MQ37/esp32-air-quality-monitor/firmware/components/lvgl_esp32_drivers/lvgl_tft/st7789.c

/**
 * @file st7789.c
 *
 * Mostly taken from lbthomsen/esp-idf-littlevgl github.
 */

#include "freertos/FreeRTOS.h"
#include "freertos/task.h"
#include "sdkconfig.h"

#include "esp_log.h"

#include "st7789.h"

#include "disp_spi.h"
#include "driver/gpio.h"

/*********************
 *      DEFINES
 *********************/
#define TAG "st7789"
/**********************
 *      TYPEDEFS
 **********************/

/*The LCD needs a bunch of command/argument values to be initialized. They are stored in this struct. */
typedef struct {
    uint8_t cmd;
    uint8_t data[16];
    uint8_t databytes; //No of data in data; bit 7 = delay after set; 0xFF = end of cmds.
} lcd_init_cmd_t;

/**********************
 *  STATIC PROTOTYPES
 **********************/
static void st7789_set_orientation(uint8_t orientation);

static void st7789_send_color(void *data, size_t length);

/**********************
 *  STATIC VARIABLES
 **********************/

/**********************
 *      MACROS
 **********************/

/**********************
 *   GLOBAL FUNCTIONS
 **********************/
void st7789_init(void)
{
    /*
     * Init sequence for the ST7789P3 IPS panel on the ESP32-32E / E32R32P board.
     * Register values match the panel vendor's example code; see
     * docs/display-init.md in the project root for background.
     * databytes: number of parameter bytes; bit 7 set = wait 100 ms afterwards.
     */
    lcd_init_cmd_t st7789_init_cmds[] = {
        {ST7789_MADCTL, {0x00}, 1},                     // memory access order; replaced by st7789_set_orientation() below
        {ST7789_COLMOD, {0x05}, 1},                     // 16 bits per pixel (RGB565)
        {ST7789_PORCTRL, {0x0C, 0x0C, 0x00, 0x33, 0x33}, 5}, // porch (blanking) timing
        {ST7789_GCTRL, {0x74}, 1},                      // gate driver voltages VGH/VGL
        {ST7789_VCOMS, {0x13}, 1},                      // VCOM voltage (vendor value; 0x23 was less stable here)
        {ST7789_LCMCTRL, {0x2C}, 1},                    // LCM control
        {ST7789_VDVVRHEN, {0x01}, 1},                   // take VDV/VRH from the next two commands
        {ST7789_VRHS, {0x10}, 1},                       // VRH: gamma reference voltage
        {ST7789_VDVSET, {0x20}, 1},                     // VDV: voltage offset
        {ST7789_FRCTR2, {0x0F}, 1},                     // frame rate in normal mode (0x0F = 60 Hz)
        {ST7789_PWCTRL1, {0xA4, 0xA1}, 2},              // power control 1 (AVDD/AVCL/VDS)
        {0xD6, {0xA1}, 1},                              // vendor-specific, kept as in the vendor code
        {ST7789_PVGAMCTRL, {0xD0, 0x07, 0x0E, 0x0B, 0x0A, 0x14, 0x38, 0x33, 0x4F, 0x37, 0x16, 0x16, 0x2A, 0x2E}, 14}, // positive gamma curve
        {ST7789_NVGAMCTRL, {0xD0, 0x0B, 0x10, 0x08, 0x08, 0x06, 0x35, 0x54, 0x4D, 0x0A, 0x14, 0x14, 0x2C, 0x2F}, 14}, // negative gamma curve
        {ST7789_EQCTRL, {0x11, 0x11, 0x03}, 3},         // equalize time control
#if ST7789_INVERT_COLORS == 1
        {ST7789_INVON, {0}, 0},                         // inversion on: needed for correct colours on this IPS panel
#else
        {ST7789_INVOFF, {0}, 0},
#endif
        {ST7789_SLPOUT, {0}, 0x80},                     // leave sleep mode, then wait
        {ST7789_DISPON, {0}, 0x80},                     // display on, then wait
        {0, {0}, 0xff},
    };

    //Initialize non-SPI GPIOs
    esp_rom_gpio_pad_select_gpio(ST7789_DC);
    gpio_set_direction(ST7789_DC, GPIO_MODE_OUTPUT);

#if !defined(ST7789_SOFT_RST)
    esp_rom_gpio_pad_select_gpio(ST7789_RST);
    gpio_set_direction(ST7789_RST, GPIO_MODE_OUTPUT);

    //Reset the display
    gpio_set_level(ST7789_RST, 0);
    vTaskDelay(100 / portTICK_PERIOD_MS);
    gpio_set_level(ST7789_RST, 1);
    vTaskDelay(100 / portTICK_PERIOD_MS);
#else
    // No reset GPIO: on the ESP32-32E the panel reset is tied to the ESP32 EN
    // pin, so send a software reset and give the controller time to restart.
    st7789_send_cmd(ST7789_SWRESET);
    vTaskDelay(150 / portTICK_PERIOD_MS);
#endif

    ESP_LOGI(TAG, "ST7789 initialization.");

    //Send all the commands
    uint16_t cmd = 0;
    while (st7789_init_cmds[cmd].databytes!=0xff) {
        st7789_send_cmd(st7789_init_cmds[cmd].cmd);
        st7789_send_data(st7789_init_cmds[cmd].data, st7789_init_cmds[cmd].databytes&0x1F);
        if (st7789_init_cmds[cmd].databytes & 0x80) {
                vTaskDelay(100 / portTICK_PERIOD_MS);
        }
        cmd++;
    }

    st7789_set_orientation(CONFIG_LV_DISPLAY_ORIENTATION);
}

/* The ST7789 display controller can drive up to 320*240 displays, when using a 240*240 or 240*135
 * displays there's a gap of 80px or 40/52/53px respectively. 52px or 53x offset depends on display orientation.
 * We need to edit the coordinates to take into account those gaps, this is not necessary in all orientations. */
void st7789_flush(lv_disp_drv_t * drv, const lv_area_t * area, lv_color_t * color_map)
{
    uint8_t data[4] = {0};

    uint16_t offsetx1 = area->x1;
    uint16_t offsetx2 = area->x2;
    uint16_t offsety1 = area->y1;
    uint16_t offsety2 = area->y2;

#if (CONFIG_LV_TFT_DISPLAY_OFFSETS)
    offsetx1 += CONFIG_LV_TFT_DISPLAY_X_OFFSET;
    offsetx2 += CONFIG_LV_TFT_DISPLAY_X_OFFSET;
    offsety1 += CONFIG_LV_TFT_DISPLAY_Y_OFFSET;
    offsety2 += CONFIG_LV_TFT_DISPLAY_Y_OFFSET;

#elif (LV_HOR_RES_MAX == 240) && (LV_VER_RES_MAX == 240)
    #if (CONFIG_LV_DISPLAY_ORIENTATION_PORTRAIT)
        offsetx1 += 80;
        offsetx2 += 80;
    #elif (CONFIG_LV_DISPLAY_ORIENTATION_LANDSCAPE_INVERTED)
        offsety1 += 80;
        offsety2 += 80;
    #endif
#elif (LV_HOR_RES_MAX == 240) && (LV_VER_RES_MAX == 135)
    #if (CONFIG_LV_DISPLAY_ORIENTATION_PORTRAIT) || \
        (CONFIG_LV_DISPLAY_ORIENTATION_PORTRAIT_INVERTED)
        offsetx1 += 40;
        offsetx2 += 40;
        offsety1 += 53;
        offsety2 += 53;
    #endif
#elif (LV_HOR_RES_MAX == 135) && (LV_VER_RES_MAX == 240)
    #if (CONFIG_LV_DISPLAY_ORIENTATION_LANDSCAPE) || \
        (CONFIG_LV_DISPLAY_ORIENTATION_LANDSCAPE_INVERTED)
        offsetx1 += 52;
        offsetx2 += 52;
        offsety1 += 40;
        offsety2 += 40;
    #endif
#endif

    /*Column addresses*/
    st7789_send_cmd(ST7789_CASET);
    data[0] = (offsetx1 >> 8) & 0xFF;
    data[1] = offsetx1 & 0xFF;
    data[2] = (offsetx2 >> 8) & 0xFF;
    data[3] = offsetx2 & 0xFF;
    st7789_send_data(data, 4);

    /*Page addresses*/
    st7789_send_cmd(ST7789_RASET);
    data[0] = (offsety1 >> 8) & 0xFF;
    data[1] = offsety1 & 0xFF;
    data[2] = (offsety2 >> 8) & 0xFF;
    data[3] = offsety2 & 0xFF;
    st7789_send_data(data, 4);

    /*Memory write*/
    st7789_send_cmd(ST7789_RAMWR);

    size_t size = (size_t)lv_area_get_width(area) * (size_t)lv_area_get_height(area);

    st7789_send_color((void*)color_map, size * 2);

}

/**********************
 *   STATIC FUNCTIONS
 **********************/
void st7789_send_cmd(uint8_t cmd)
{
    disp_wait_for_pending_transactions();
    gpio_set_level(ST7789_DC, 0);
    disp_spi_send_data(&cmd, 1);
}

void st7789_send_data(void * data, uint16_t length)
{
    disp_wait_for_pending_transactions();
    gpio_set_level(ST7789_DC, 1);
    disp_spi_send_data(data, length);
}

static void st7789_send_color(void * data, size_t length)
{
    disp_wait_for_pending_transactions();
    gpio_set_level(ST7789_DC, 1);
    disp_spi_send_colors(data, length);
}

static void st7789_set_orientation(uint8_t orientation)
{
    // ESP_ASSERT(orientation < 4);

    const char *orientation_str[] = {
        "PORTRAIT", "PORTRAIT_INVERTED", "LANDSCAPE", "LANDSCAPE_INVERTED"
    };

    ESP_LOGI(TAG, "Display orientation: %s", orientation_str[orientation]);

    // MADCTL values per orientation. The first two (portrait / portrait
    // inverted) are swapped compared to upstream to match the ESP32-32E panel;
    // this firmware uses LANDSCAPE (0x60), which is unchanged.
    uint8_t data[] =
    {
#if CONFIG_LV_PREDEFINED_DISPLAY_TTGO
	0x60, 0xA0, 0x00, 0xC0
#else
	0x00, 0xC0, 0x60, 0xA0
#endif
    };

    ESP_LOGI(TAG, "0x36 command value: 0x%02X", data[orientation]);

    st7789_send_cmd(ST7789_MADCTL);
    st7789_send_data((void *) &data[orientation], 1);
}
